qwelyt/Keyboard/Pics/DSC02869.JPG

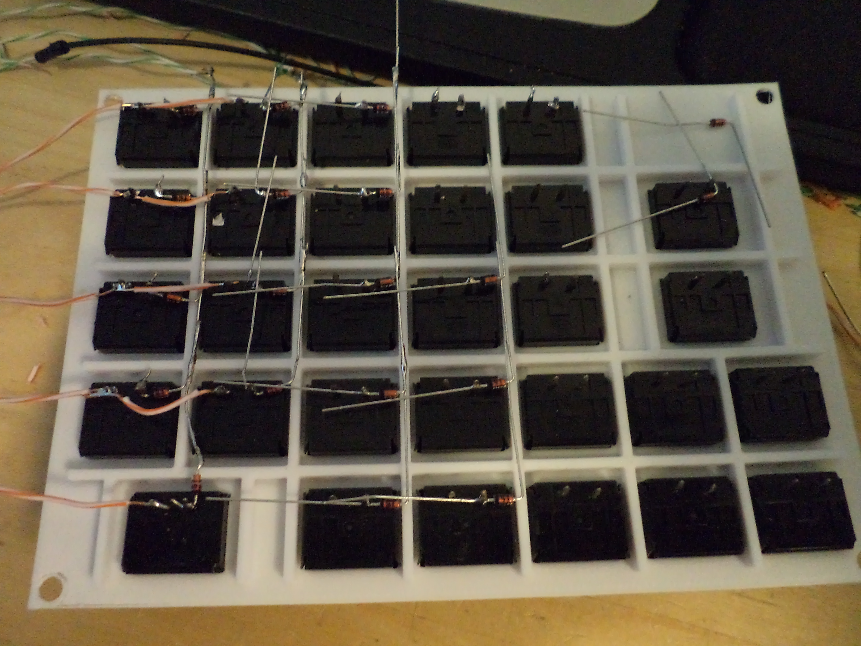
Pics/DSC02869.JPG
