qwelyt/Keyboard/Pics/DSC02870.JPG

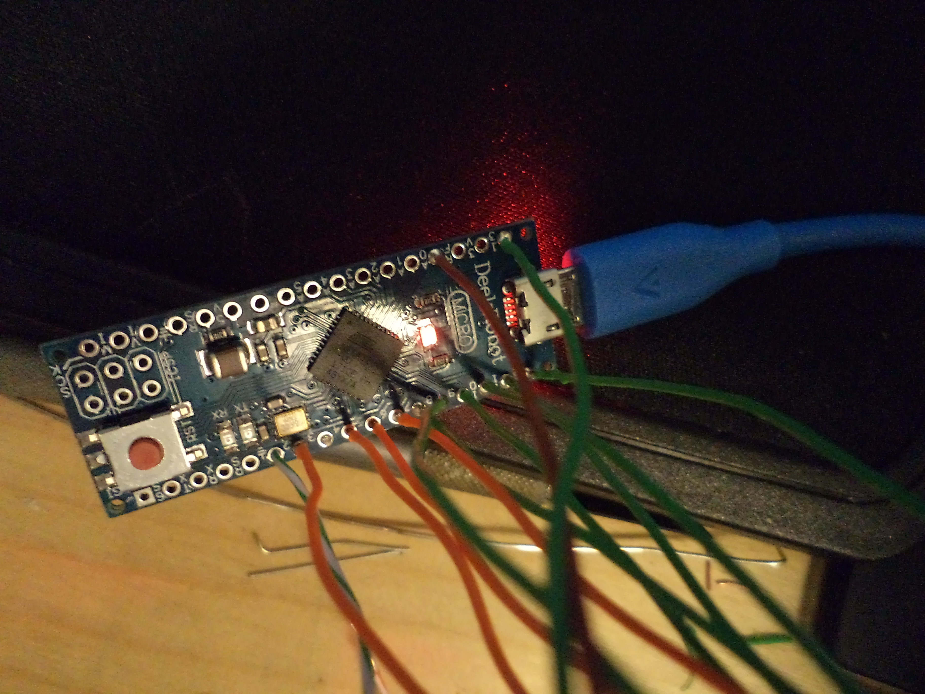
Pics/DSC02870.JPG
