qwelyt/Keyboard/Pics/DSC02872.JPG

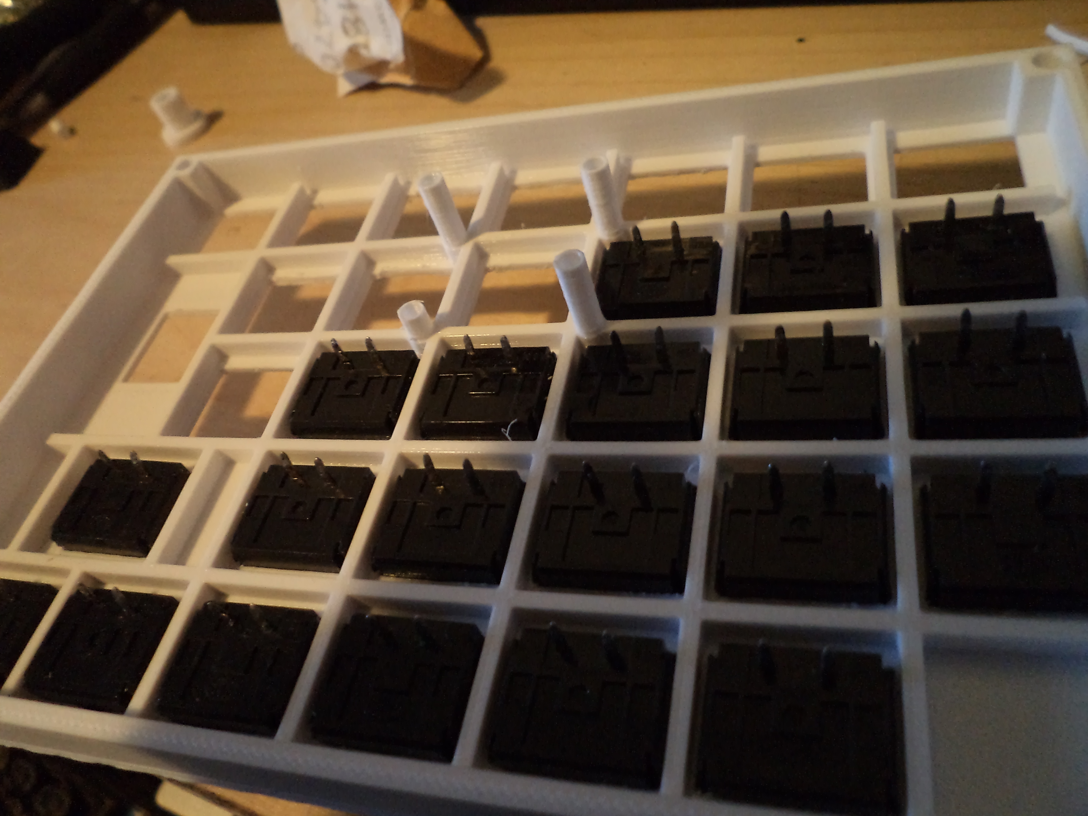
Pics/DSC02872.JPG
