qwelyt/Keyboard/Pics/DSC02873.JPG

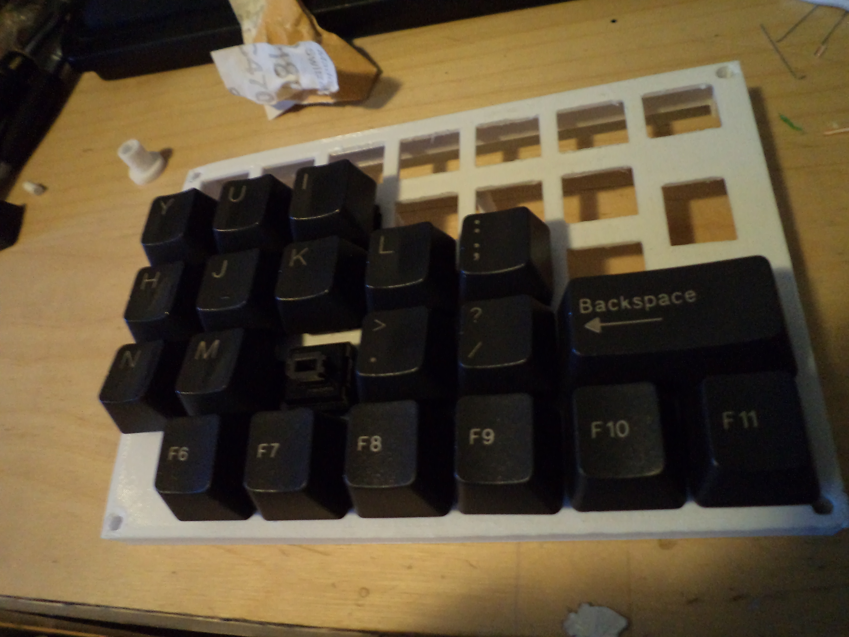
Pics/DSC02873.JPG
