qwelyt/Keyboard/Pics/DSC02874.JPG

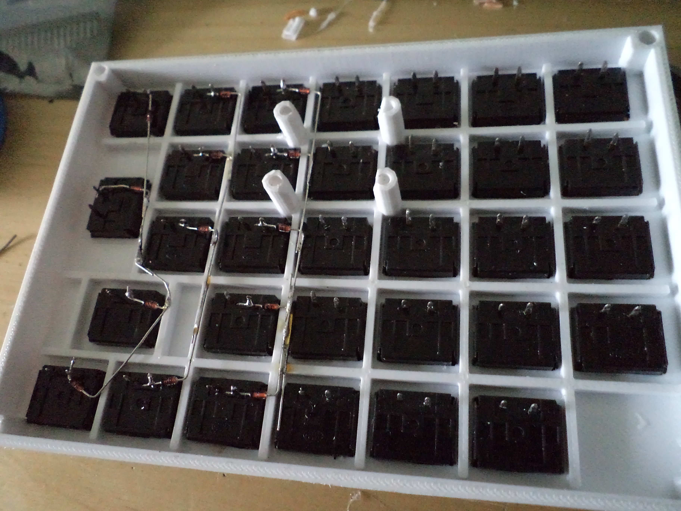
Pics/DSC02874.JPG
