qwelyt/Keyboard/Pics/DSC02875.JPG

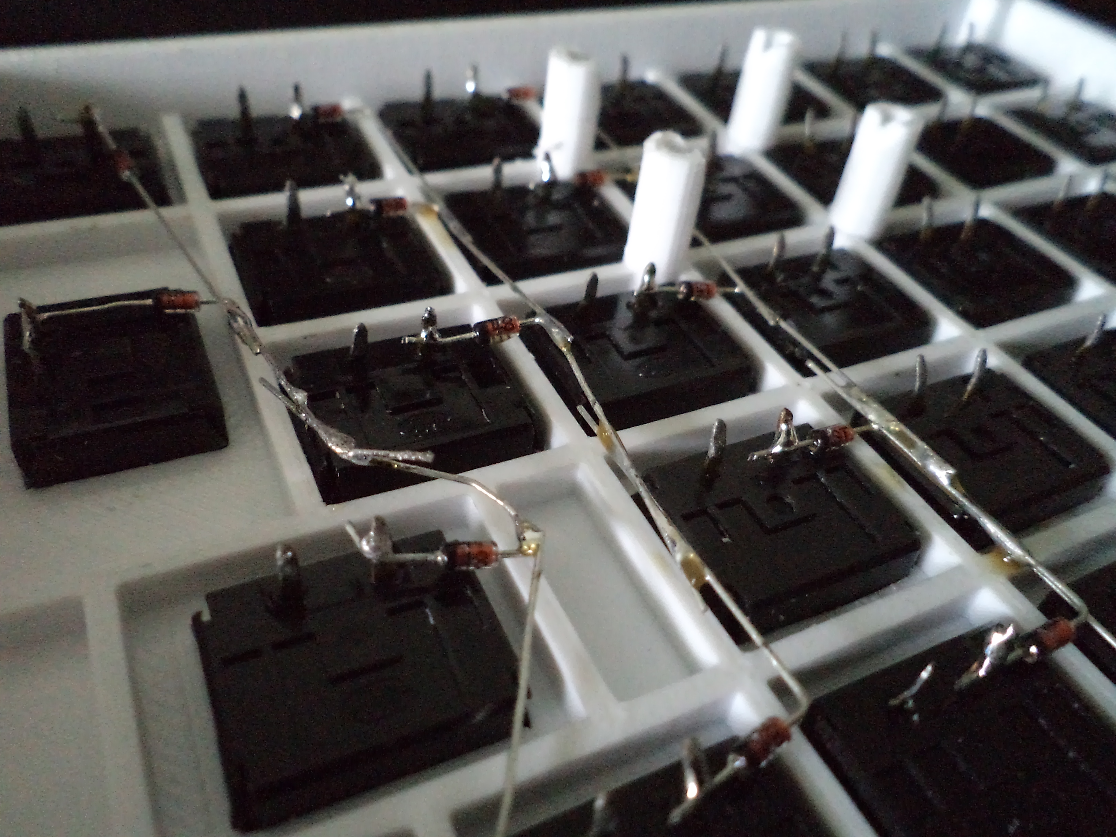
Pics/DSC02875.JPG
