qwelyt/Keyboard/Pics/DSC02876.JPG

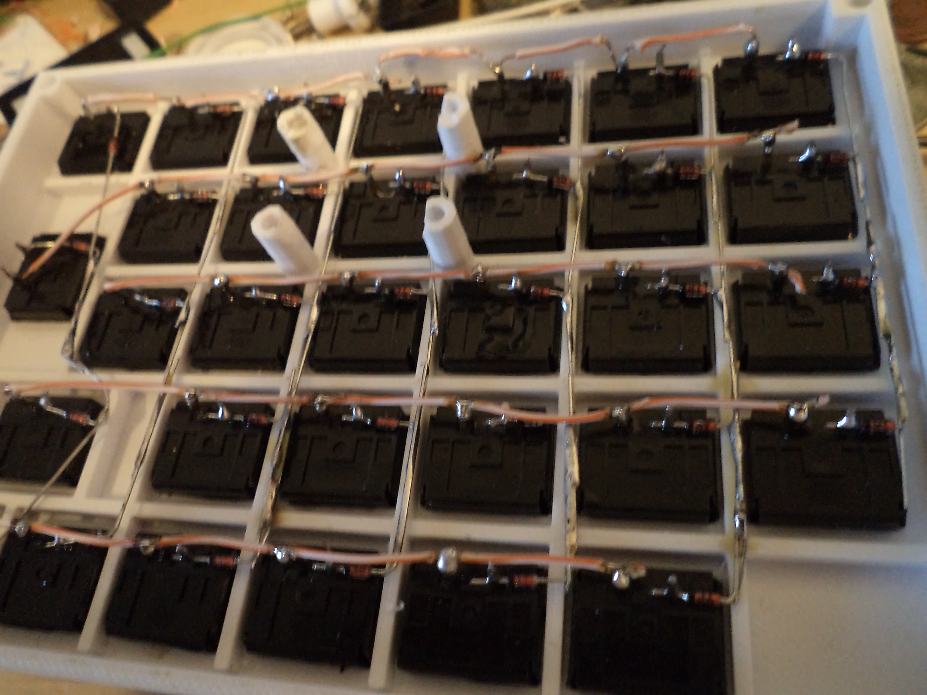
Pics/DSC02876.JPG
