qwelyt/Keyboard/Pics/DSC02878.JPG

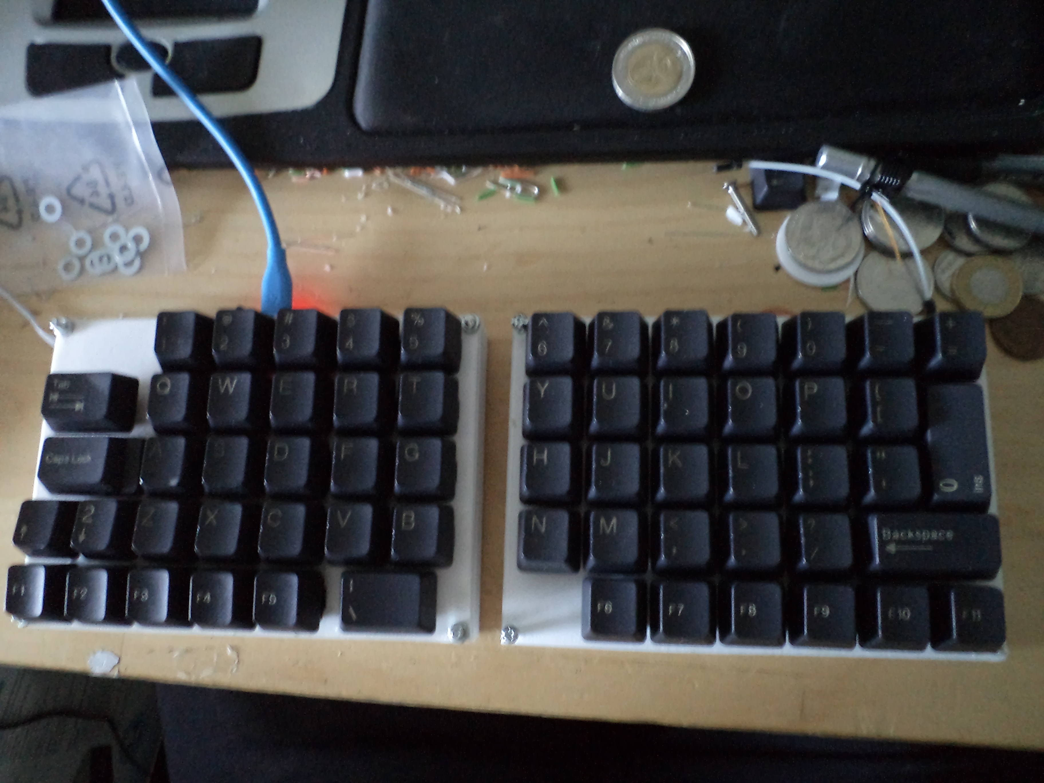
Pics/DSC02878.JPG
