qwelyt/Keyboard/Design/SCAD/KeySizeTest/KeySize_15x13.stl

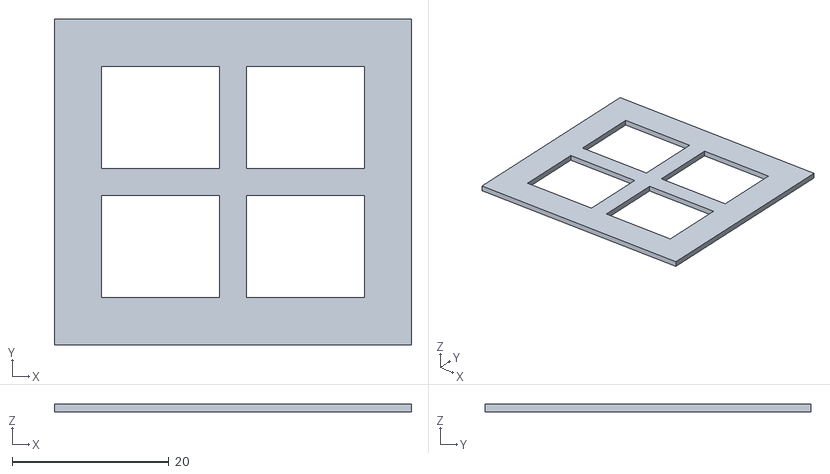
[picture p28: CAD file, 2017-05-07]
Design/SCAD/KeySizeTest/KeySize_15x13.stl
45.5 x 41.5 x 1.00
