qwelyt/Keyboard/Design/SCAD/ModuleA/V1/moduleA-top_smaller.stl

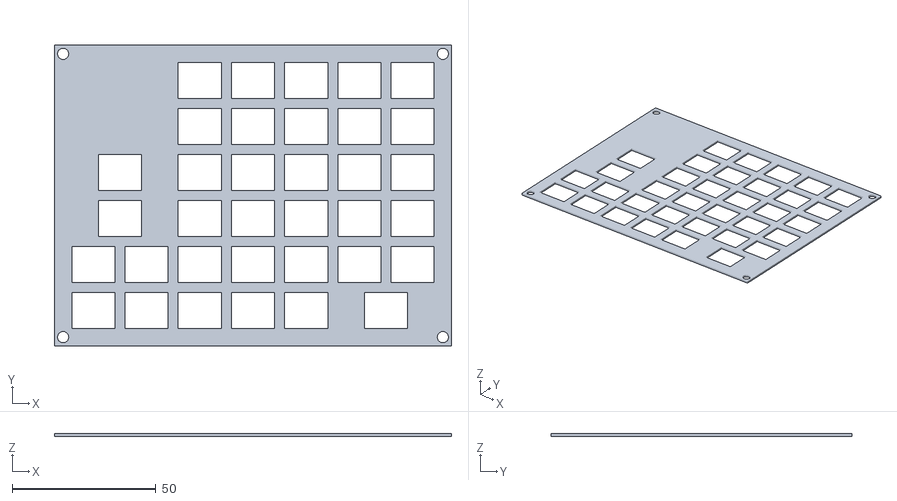
[picture p29: CAD file, 2017-05-07, an earlier design]
Design/SCAD/ModuleA/V1/moduleA-top_smaller.stl
138.0 x 104.5 x 1.00
