qwelyt/Keyboard/Code/Basics/analogBlock/analogBlock.ino

int sensorPin = A0;    // select the input pin for the potentiometer
int ledPin = 13;      // select the pin for the LED
int sensorValue = 0;  // variable to store the value coming from the sensor

void setup() {
  Serial.begin(9600);
  // declare the ledPin as an OUTPUT:
  pinMode(ledPin, OUTPUT);
  sensorValue = analogRead(sensorPin);
  Serial.println("Ready");
  while(sensorValue < 100){} // <-- Block everything if we short A0 to GND
  Serial.println("Starting");
}

void loop() {
  // read the value from the sensor:
  sensorValue = analogRead(sensorPin);
  Serial.println(sensorValue);
  // turn the ledPin on
  digitalWrite(ledPin, HIGH);
  // stop the program for <sensorValue> milliseconds:
  delay(sensorValue);
  // turn the ledPin off:
  digitalWrite(ledPin, LOW);
  // stop the program for for <sensorValue> milliseconds:
  delay(sensorValue);
}
